Robert-Riordan-UCD/8_Bit_CPU_PCB/RAM/atmega_ram_emulator/atmega_ram_emulator.ino

#include "PinChangeInterrupt.h"

// Set to true to use the top 4 bits of memory instead of the bottom 4 bits
#define HIGH_NIBBLE true

/* Memory preloaded with instructions to coutn in 3s */
uint8_t memory[16] = {
  0b00011111, // (LDA) 15
  0b00101110, // (ADD) 14
  0b11100000, // (OUT)
  0b01100001, // (JMP)  1
  0, 0, 0, 0, 0, 0, 0, 0, 0, 0, // NOOP
  3, // 3
  0, // 0
}; // High nibble to be used by if HIGH_NIBBLE is set. Otherwise low nibble will be used

int address_pins[4] = {A0, A1, A2, A3};
int data_output_pins[4] = {5, 4, 3, 2};
int data_input_pins[4] = {7, 6, 9, 10};

int n_write_enable_pin = 8; // Write when low. Read when high

void writeToRAM () {
  for (int i = 0; i < 4; i++) { // Set output to high impedence when not in use
    pinMode(data_output_pins[i], INPUT);
  }
  
  uint16_t address = digitalRead(address_pins[0]) + 2*digitalRead(address_pins[1]) + 4*digitalRead(address_pins[2])+8*digitalRead(address_pins[3]);
  uint8_t data_in = 
    ((uint8_t)digitalRead(data_input_pins[0])<<0) +
    ((uint8_t)digitalRead(data_input_pins[1])<<1) +
    ((uint8_t)digitalRead(data_input_pins[2])<<2) +
    ((uint8_t)digitalRead(data_input_pins[3])<<3);
  memory[address] = (data_in ^ 0b1111)<<(HIGH_NIBBLE*4);
}

void readFromRAM() {
  uint16_t address = digitalRead(address_pins[0]) + 2*digitalRead(address_pins[1]) + 4*digitalRead(address_pins[2])+8*digitalRead(address_pins[3]);
  for (int i = 0; i < 4; i++) {
    pinMode(data_output_pins[i], OUTPUT); // Change from high impedence to output
    digitalWrite(data_output_pins[i], ((memory[address]>>(HIGH_NIBBLE*4))>>i)&0x01);
  }
}

void setup() {
  for (int i = 0; i < 4; i++) {
    pinMode(address_pins[i], INPUT);
    pinMode(data_output_pins[i], INPUT); // High impedence when not in use
    pinMode(data_input_pins[i], INPUT);
  }
  pinMode(n_write_enable_pin, INPUT);

  attachPCINT(digitalPinToPCINT(n_write_enable_pin), writeToRAM, FALLING); // Write to RAM on falling edge of write enable
}

void loop() {
  readFromRAM();
}
